BastianNagler/PMT2_Koordinationswand/EI-Wiki/Diagramme/ClassDiagram.png

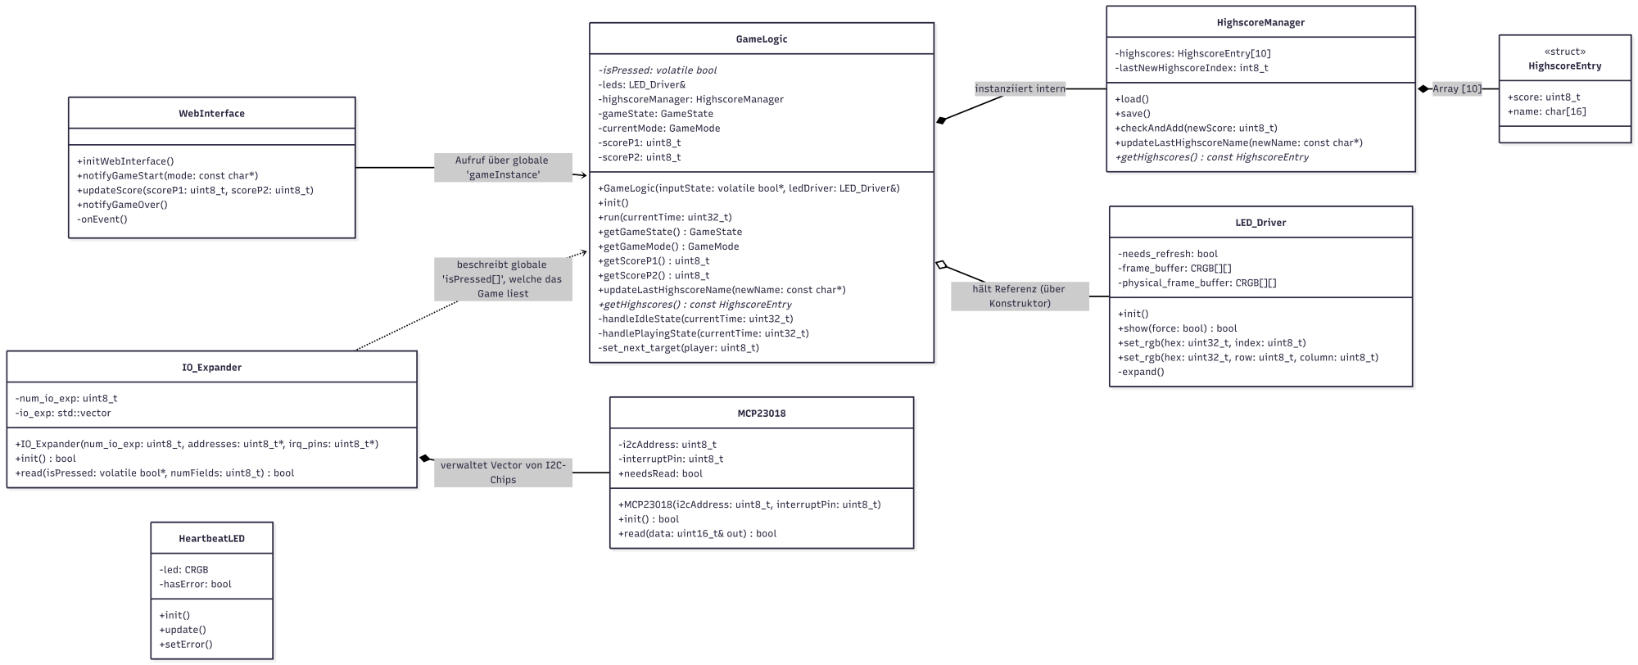
EI-Wiki/Diagramme/ClassDiagram.png
