BastianNagler/PMT2_Koordinationswand/EI-Wiki/Diagramme/Englisch/ClassDiagram.png

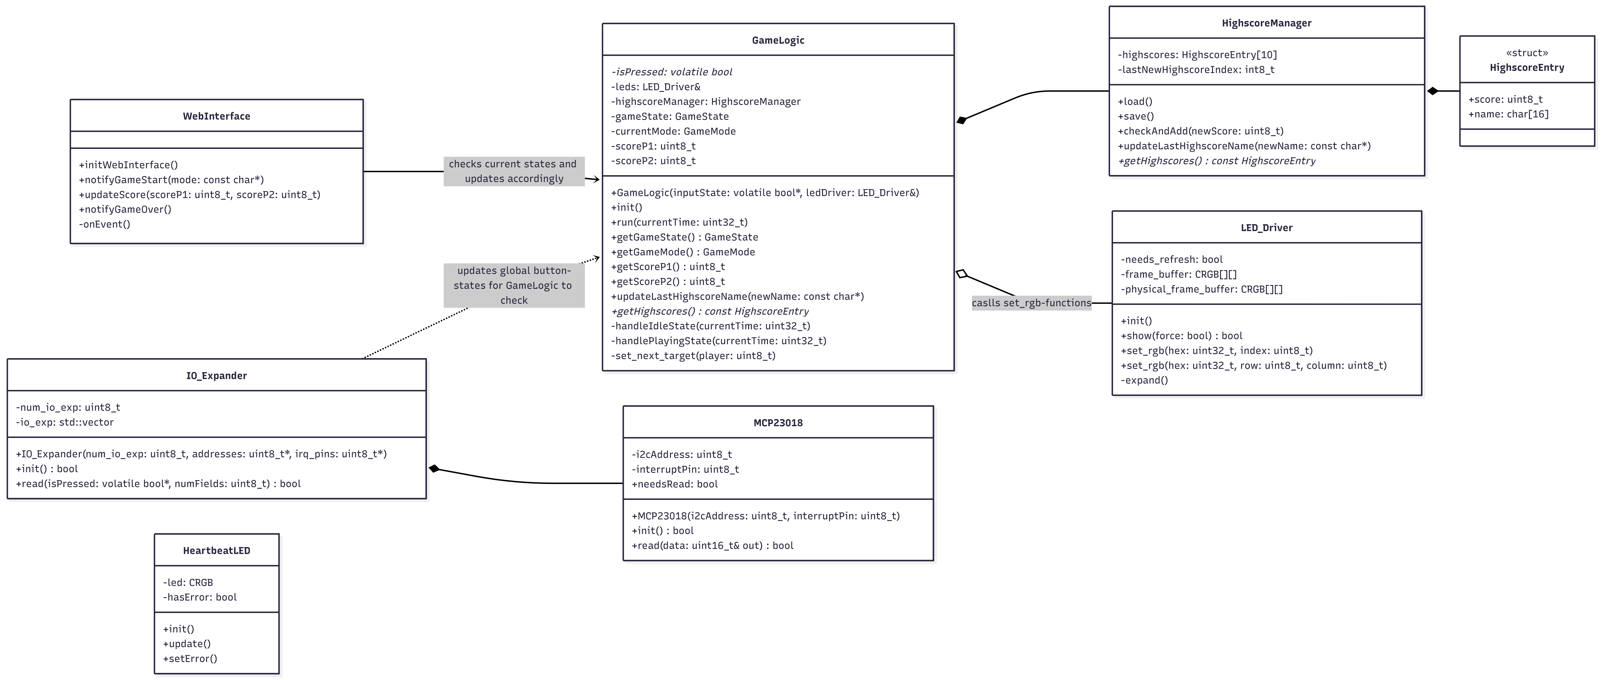
EI-Wiki/Diagramme/Englisch/ClassDiagram.png
