BastianNagler/PMT2_Koordinationswand/EI-Wiki/Diagramme/Englisch/FreeRTOS_Tasks.png

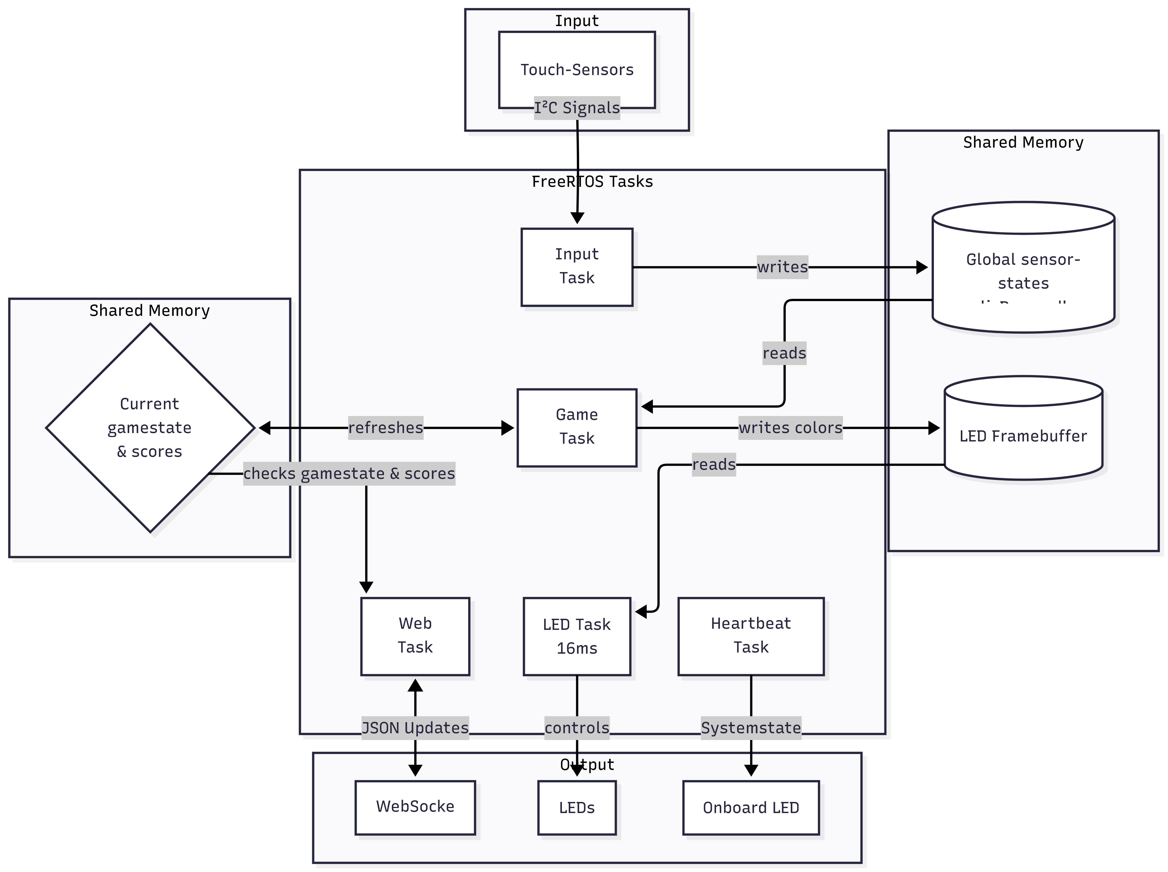
EI-Wiki/Diagramme/Englisch/FreeRTOS_Tasks.png
