BastianNagler/PMT2_Koordinationswand/EI-Wiki/Diagramme/Englisch/StateDiagram.png

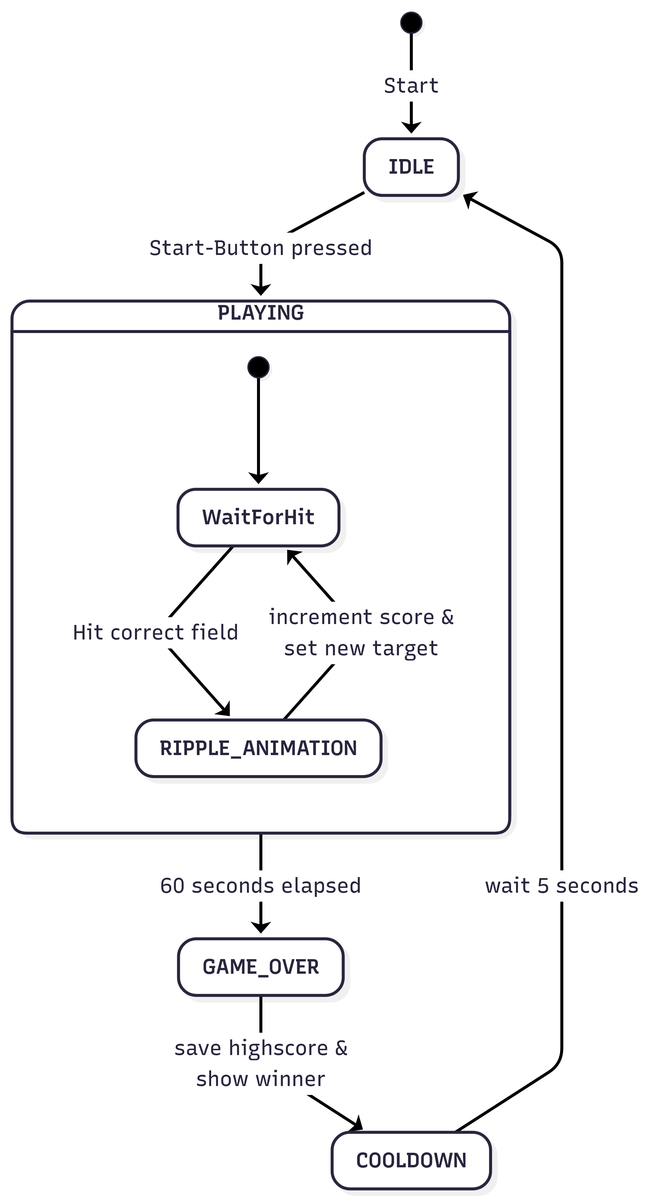
EI-Wiki/Diagramme/Englisch/StateDiagram.png
