BastianNagler/PMT2_Koordinationswand/EI-Wiki/Diagramme/StateDiagram.png

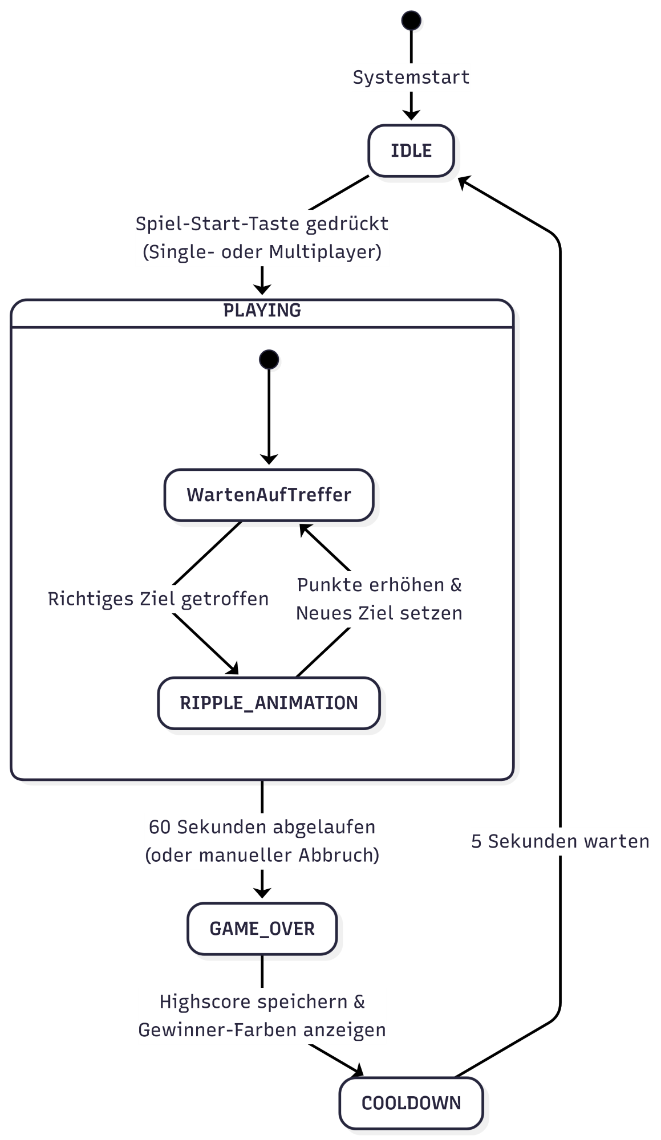
EI-Wiki/Diagramme/StateDiagram.png
