BastianNagler/PMT2_Koordinationswand/EI-Wiki/Platine/Platine_unterseite.png

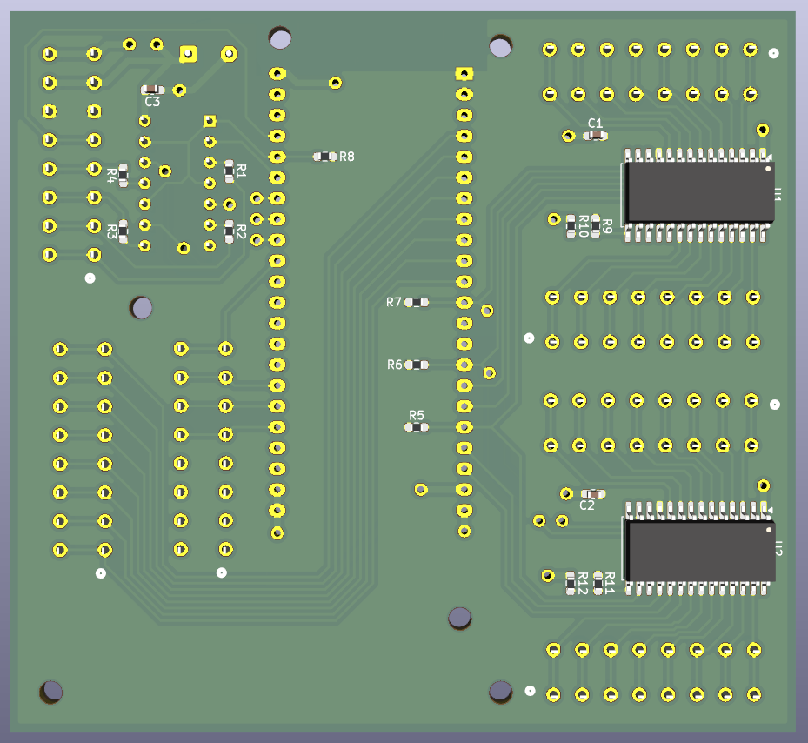
EI-Wiki/Platine/Platine_unterseite.png
