BastianNagler/PMT2_Koordinationswand/ESP32/src/heartbeat.cpp

#include "heartbeat.h"
#include "WebLog.h"

void HeartbeatLED::update()
{
    uint8_t brightness = beatsin8(30); // 30 BPM ≈ 2 Sekunden Periode

    if (hasError)
    {
        color = (brightness << 8); // Rot pulsieren
    }
    else
    {
        color = (brightness << 16); // Grün pulsieren
    }
    ws2812Write(HEARTBEAT_LED_PIN, color);
}

void HeartbeatLED::setError()
{
    WebLog.println("[HEARTBEAT] set error");
    hasError = true;
}
